CapableRobot/PMOD-Adapters/boards/BeagleWire/bottom.png

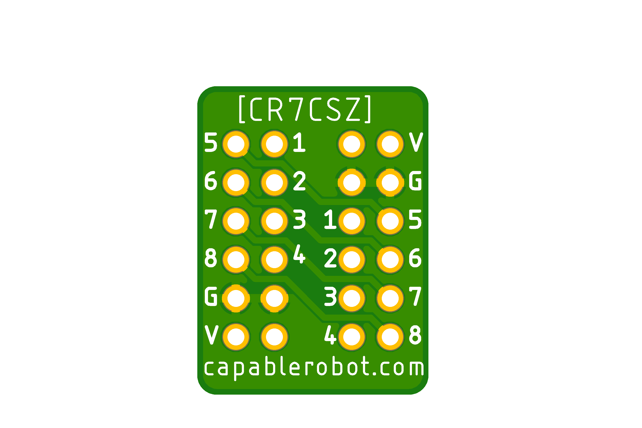
boards/BeagleWire/bottom.png
