CapableRobot/PMOD-Adapters/boards/BeagleWire/top.png

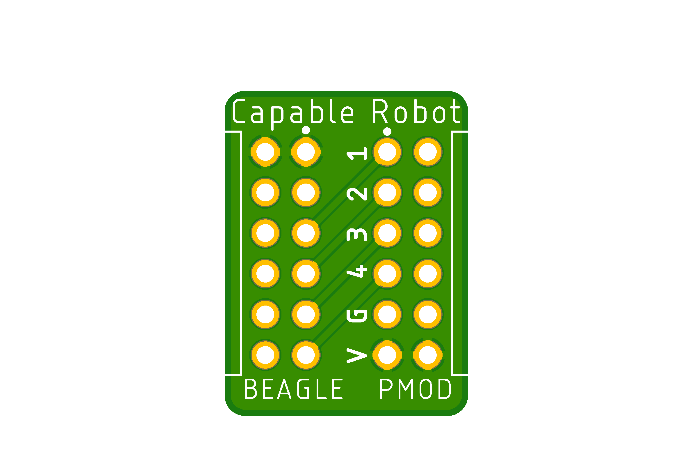
boards/BeagleWire/top.png
